tannnguyen/Autonomous-Caretaker/Design/part3rack_mirror.STL

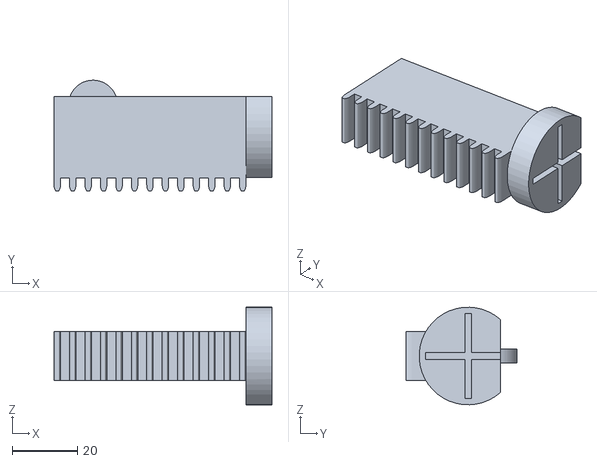
[picture p17: CAD file, 2018-12-25]
Design/part3rack_mirror.STL
67.0 x 34.0 x 30.0
