tannnguyen/Autonomous-Caretaker/Design/holder_wall_mirror.STL

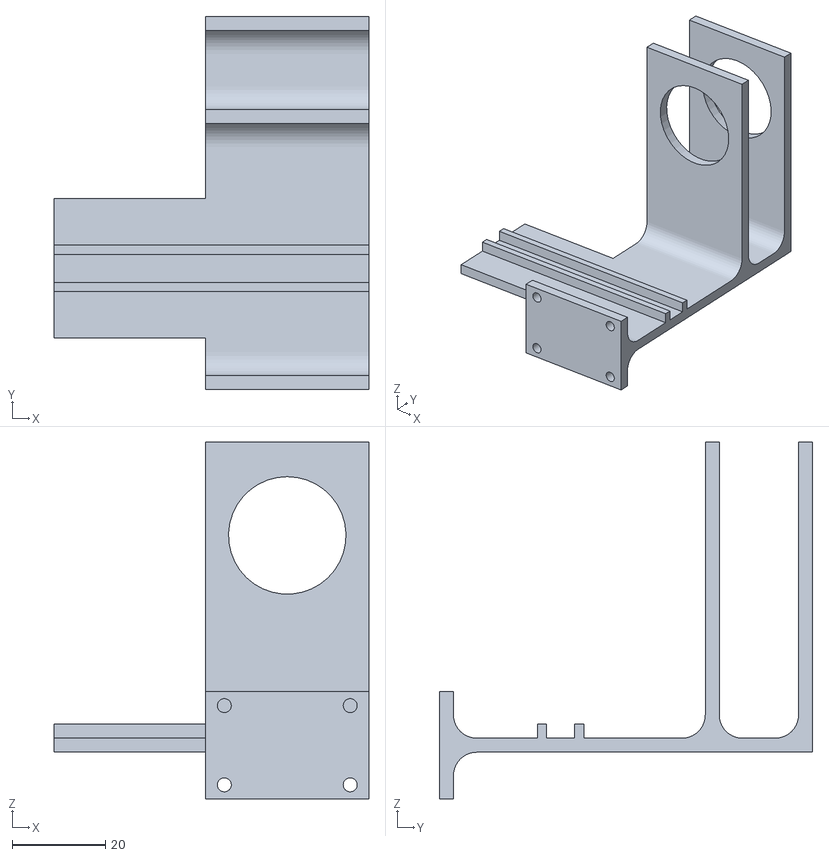
[picture p18: CAD file, 2018-12-25]
Design/holder_wall_mirror.STL
67.5 x 80.0 x 76.5
