tannnguyen/Autonomous-Caretaker/Design/motor_roller_wheel_holder_wall.SLDPRT

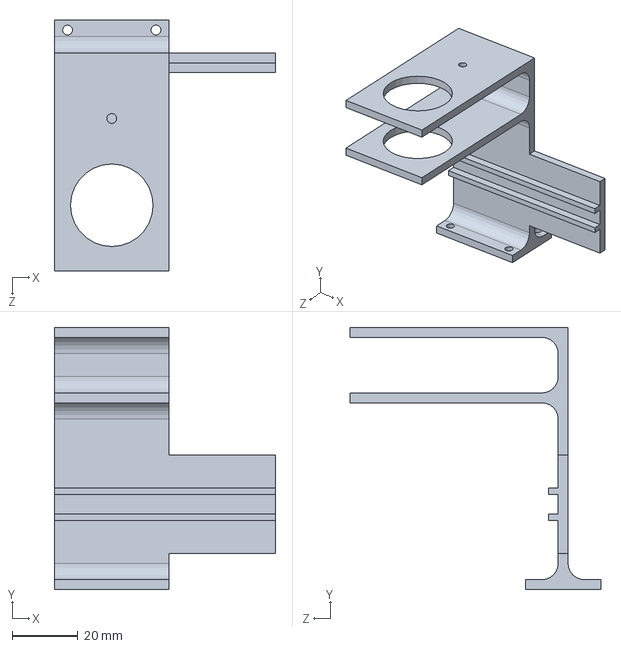
[picture p19: CAD file, 2018-12-25]
Design/motor_roller_wheel_holder_wall.SLDPRT
67.5 x 80.0 x 76.5 mm
