tannnguyen/Autonomous-Caretaker/Design/elderly_laser_cut_04_06_18.SLDPRT

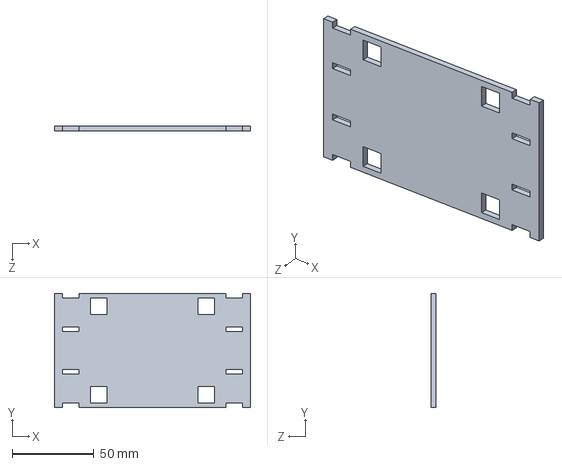
[picture p20: CAD file, 2018-12-25]
Design/elderly_laser_cut_04_06_18.SLDPRT
120.0 x 70.0 x 3.00 mm
