tannnguyen/Autonomous-Caretaker/Design/Part1pinion125_04_28.STL

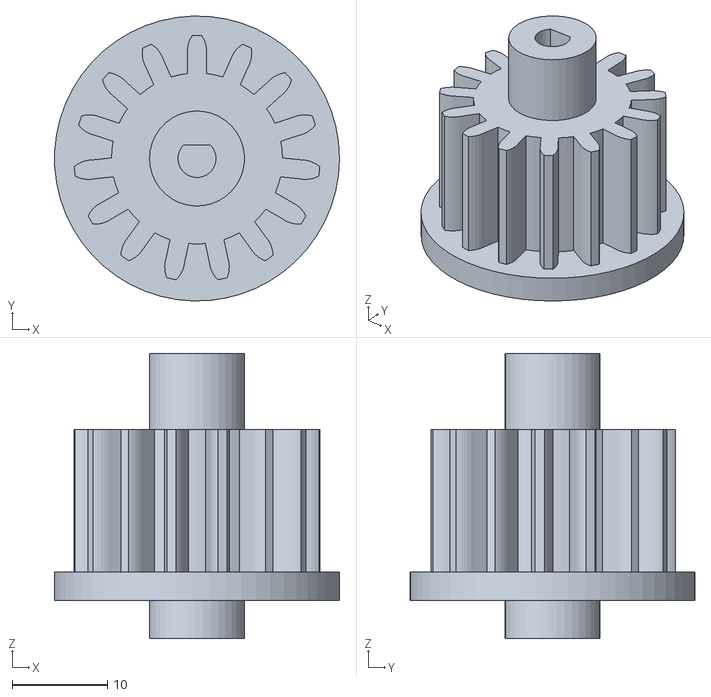
[picture p21: CAD file, 2018-12-25]
Design/Part1pinion125_04_28.STL
30.0 x 30.0 x 30.0
