tannnguyen/Autonomous-Caretaker/Design/top_chassis_04_26.SLDPRT

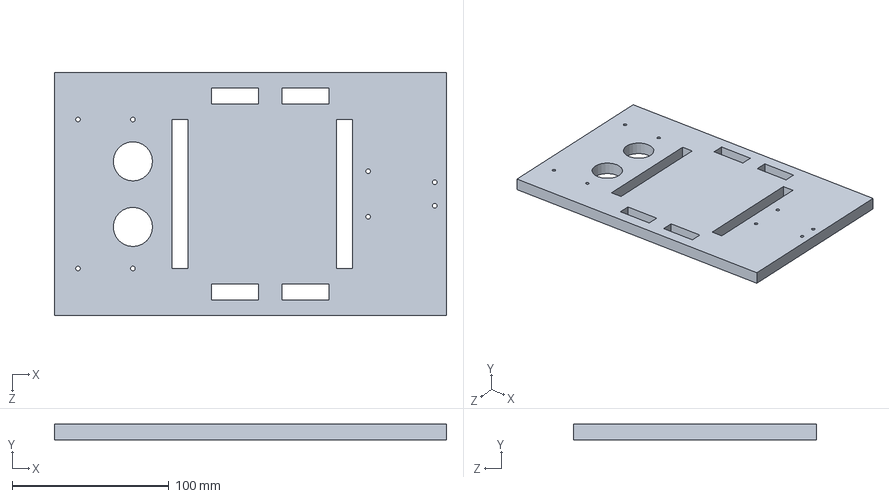
[picture p22: CAD file, 2018-12-25]
Design/top_chassis_04_26.SLDPRT
250.0 x 10.0 x 155.0 mm
