tannnguyen/Autonomous-Caretaker/Design/motor_model.SLDPRT

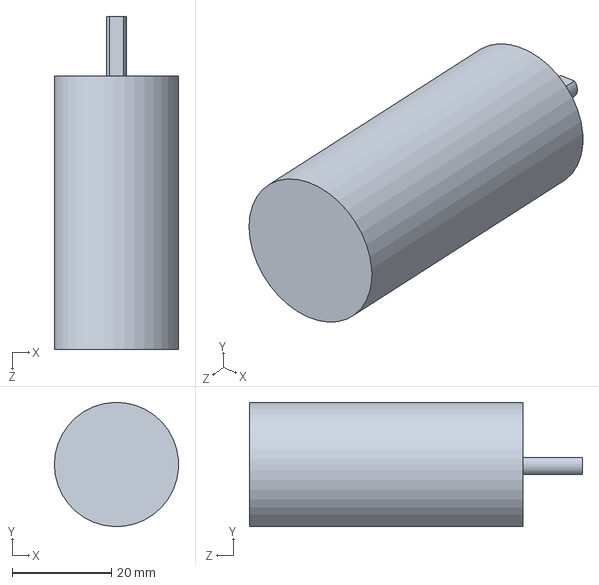
[picture p23: CAD file, 2018-12-25]
Design/motor_model.SLDPRT
25.0 x 25.0 x 67.0 mm
